Iyanuoluwa007/zetabot/3d Model/1.jpg

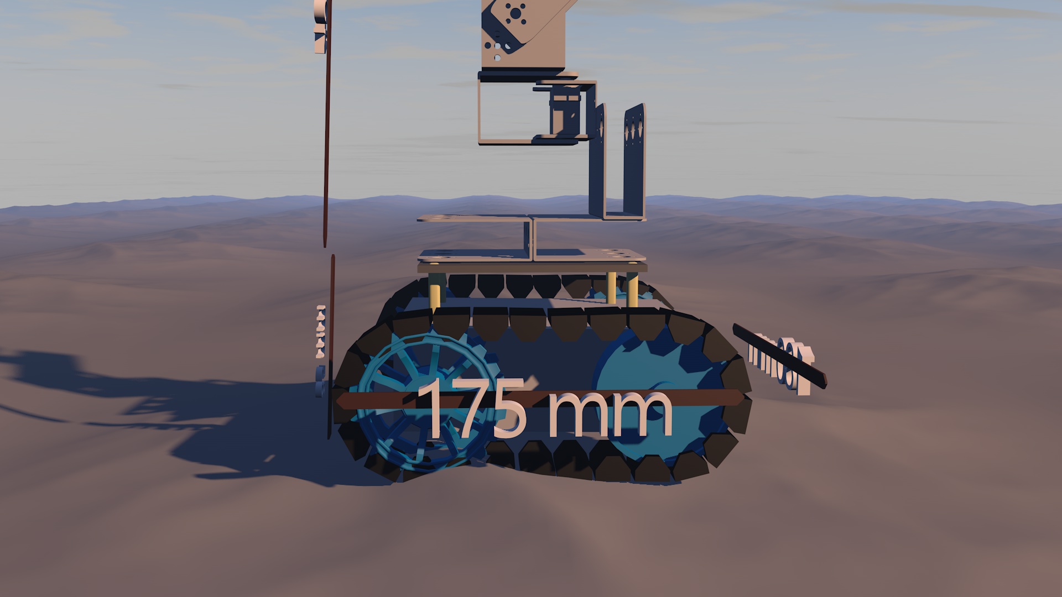
3d Model/1.jpg
