Iyanuoluwa007/zetabot/3d Model/2.jpg

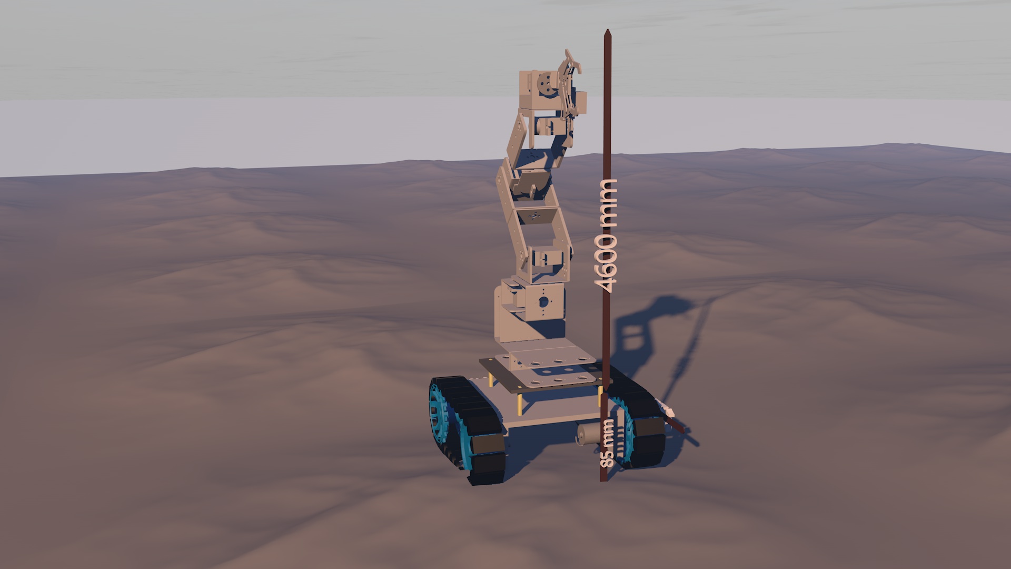
3d Model/2.jpg
