Iyanuoluwa007/zetabot/3d Model/3.jpg

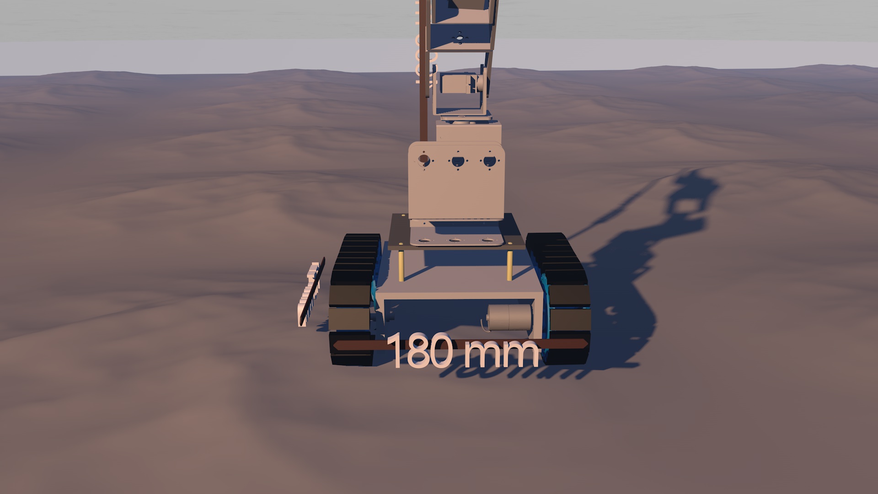
3d Model/3.jpg
