Iyanuoluwa007/zetabot/3d Model/4.jpg

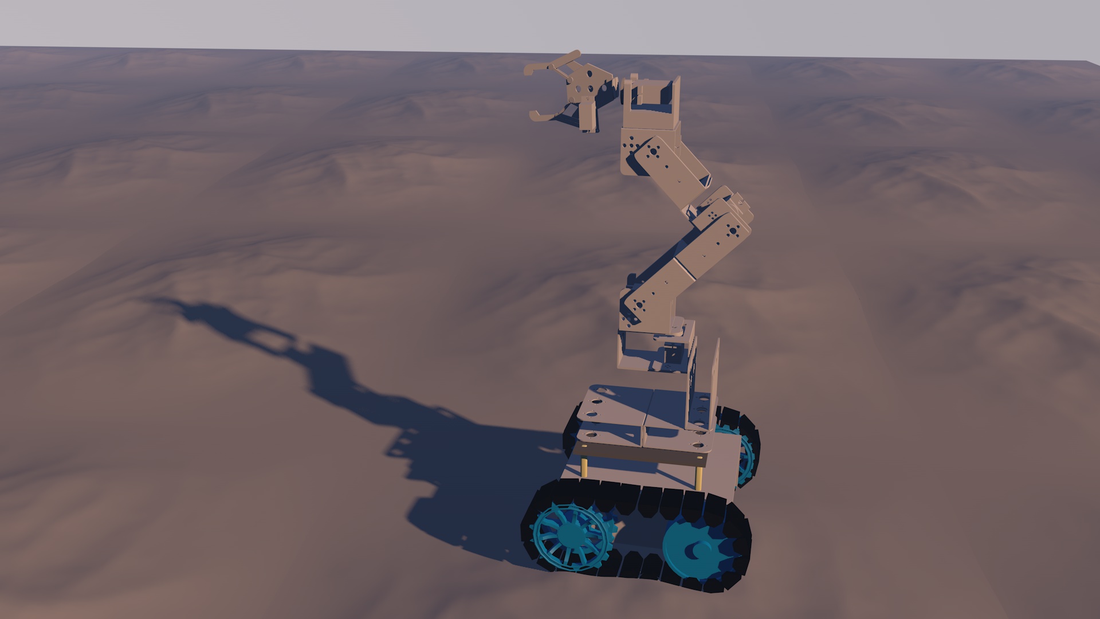
3d Model/4.jpg
