Iyanuoluwa007/zetabot/3d Model/5.jpg

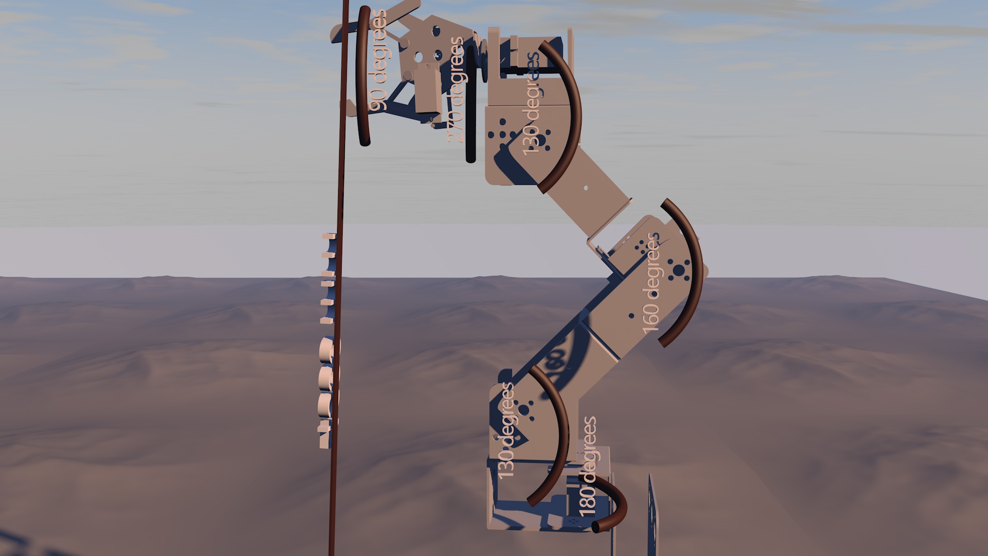
3d Model/5.jpg
