Iyanuoluwa007/zetabot/App/Robotic Arm Controller Code.png

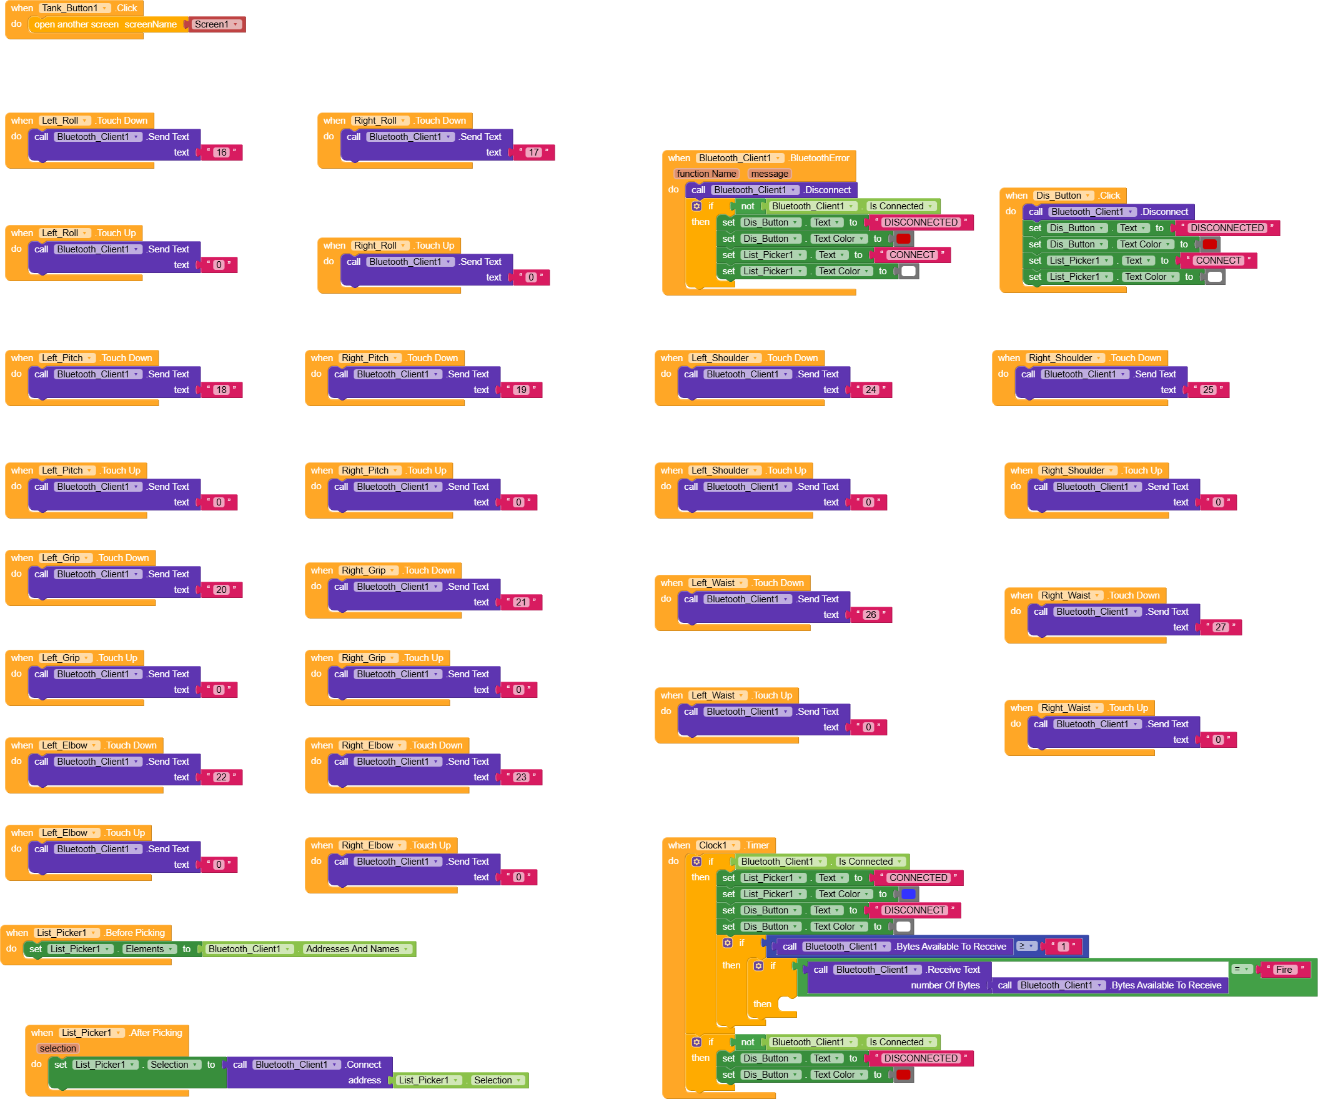
App/Robotic Arm Controller Code.png
