Iyanuoluwa007/zetabot/App/Robotic Tank Controller Code.png

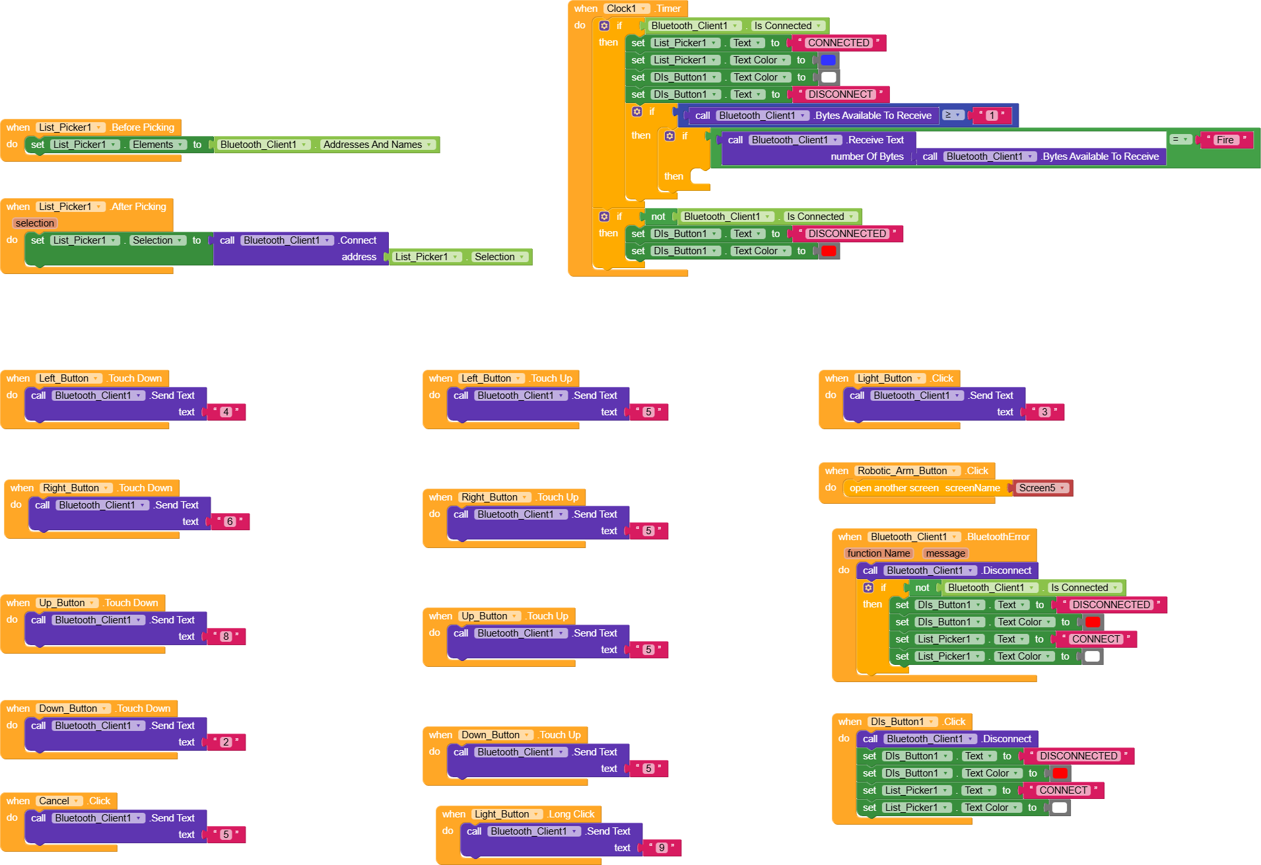
App/Robotic Tank Controller Code.png
