Iyanuoluwa007/zetabot/Documentations/xl6019 module.jpg

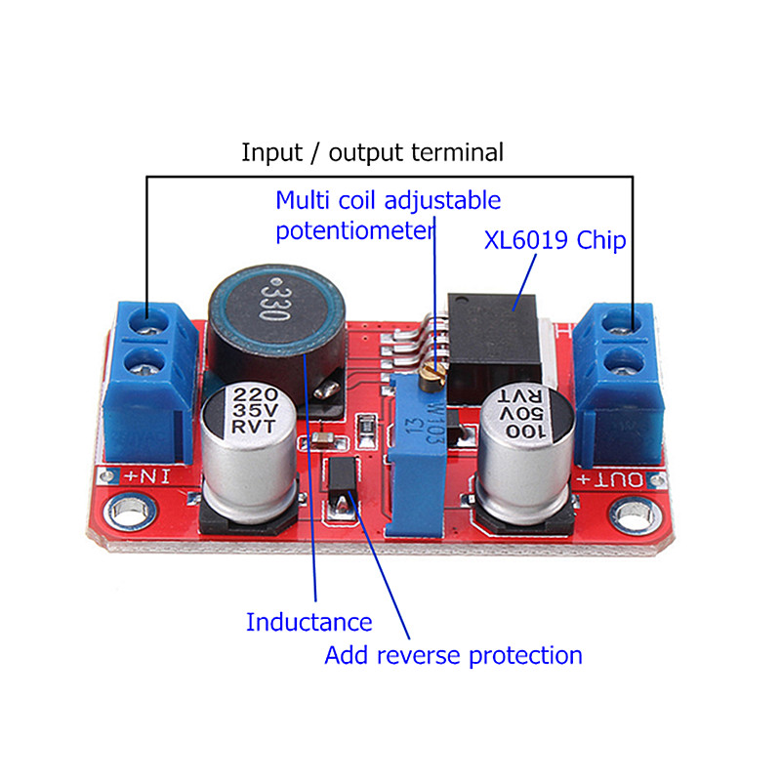
Documentations/xl6019 module.jpg
