Iyanuoluwa007/zetabot/Ideas/iron-ox-farming-robot.jpg

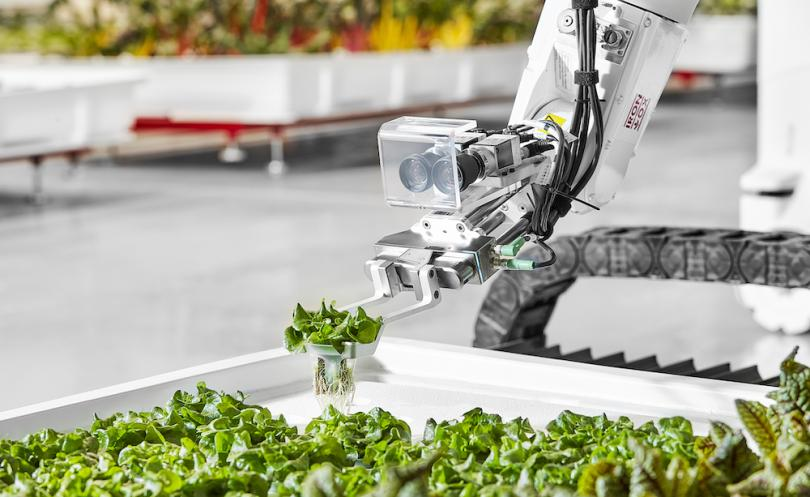
Ideas/iron-ox-farming-robot.jpg
