Iyanuoluwa007/zetabot/Plans/Robot ARM/ARM.jpg

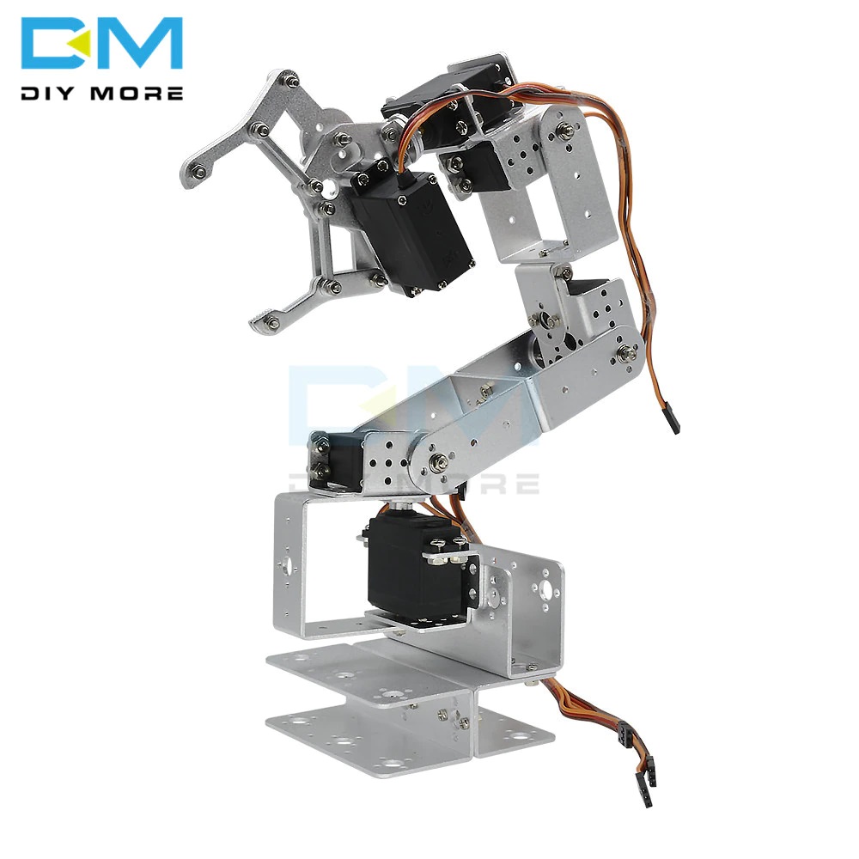
Plans/Robot ARM/ARM.jpg
