Iyanuoluwa007/zetabot/Plans/Robot ARM/H266de6f652d54e7d96e25e7c5b8f142fn.webp

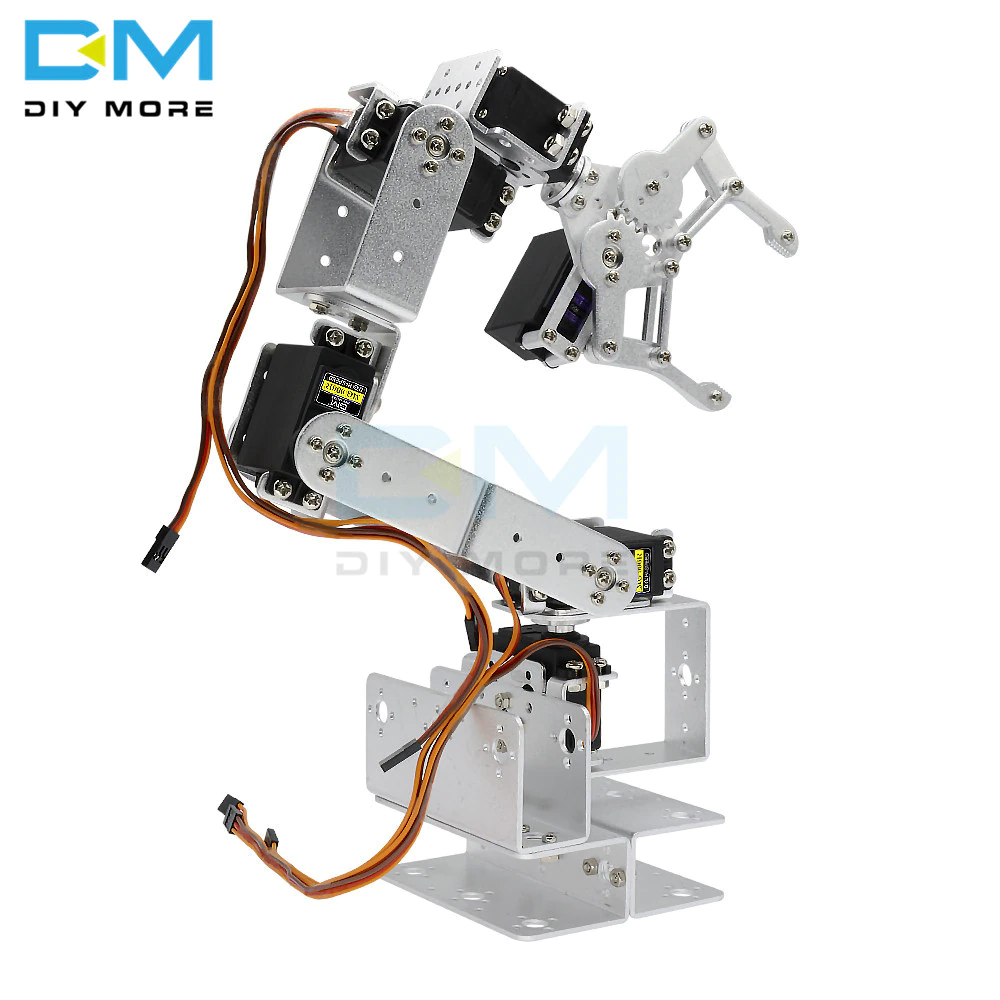
Plans/Robot ARM/H266de6f652d54e7d96e25e7c5b8f142fn.webp
