Iyanuoluwa007/zetabot/Plans/Tank/HTB1DEFNXvvsK1RjSspdq6AZepXag.webp

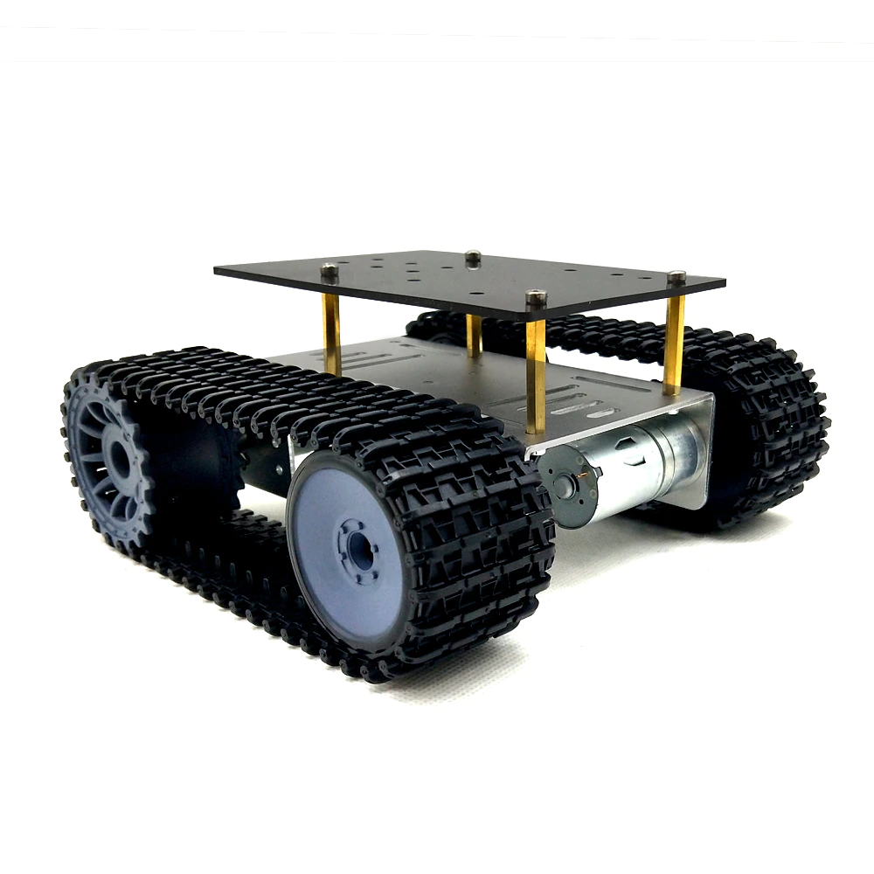
Plans/Tank/HTB1DEFNXvvsK1RjSspdq6AZepXag.webp
