Iyanuoluwa007/zetabot/Plans/Tank/HTB1HbVOXynrK1Rjy1Xcq6yeDVXaf.webp

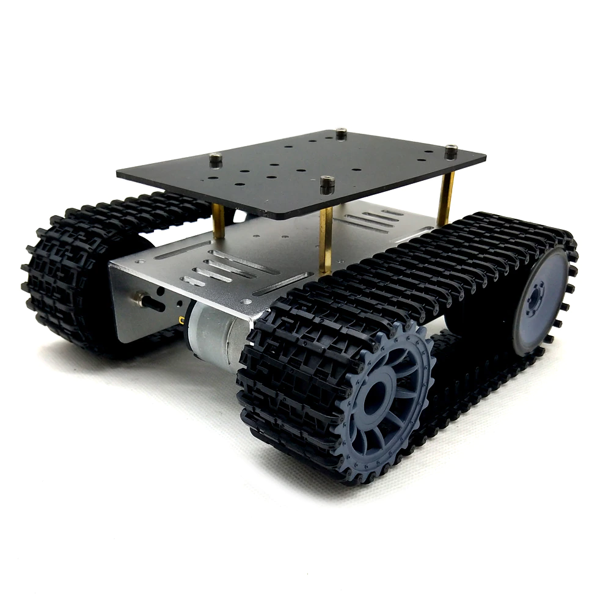
Plans/Tank/HTB1HbVOXynrK1Rjy1Xcq6yeDVXaf.webp
