Iyanuoluwa007/zetabot/Plans/Tank/HTB1tVsih6TpK1RjSZKPq6y3UpXaW.webp

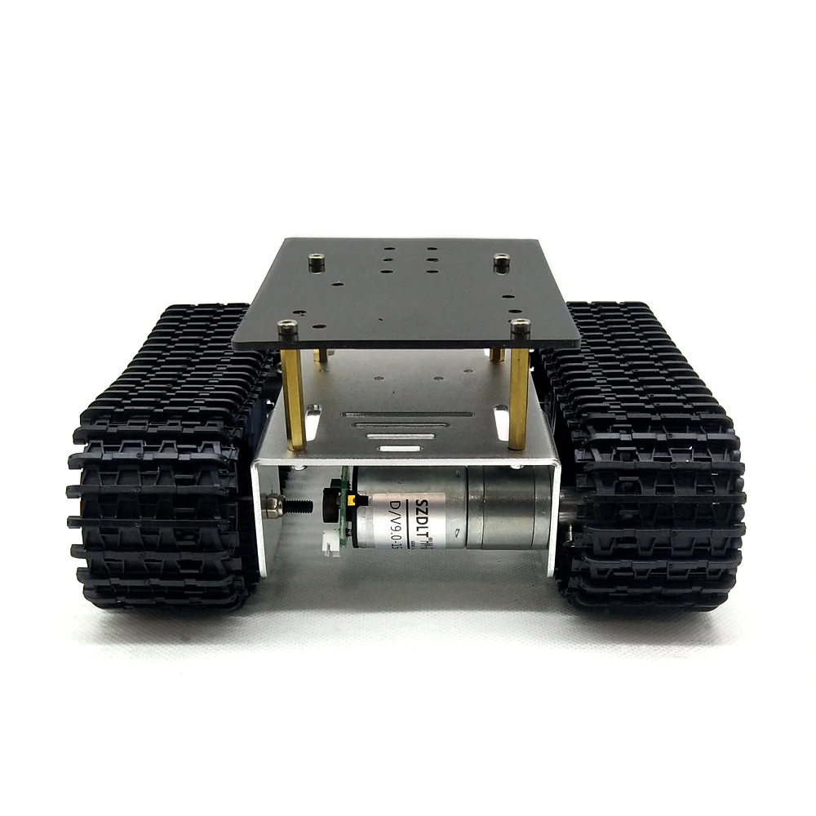
Plans/Tank/HTB1tVsih6TpK1RjSZKPq6y3UpXaW.webp
