Iyanuoluwa007/zetabot/Plans/Tank/Motor Specifications.jpg

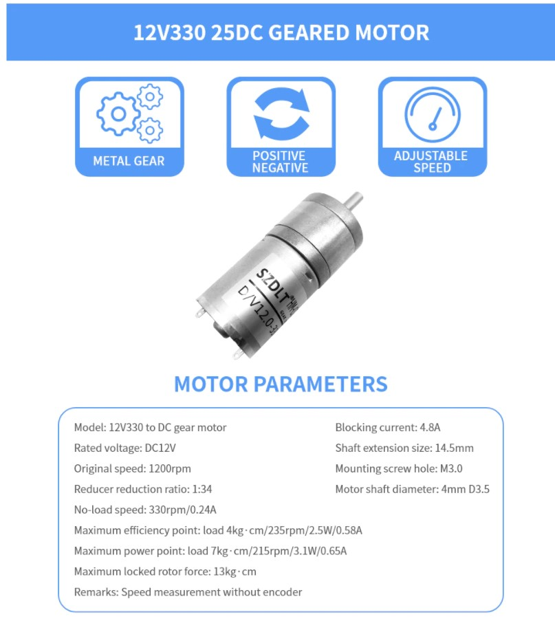
Plans/Tank/Motor Specifications.jpg
