Iyanuoluwa007/zetabot/Building/20210622_141823.jpg

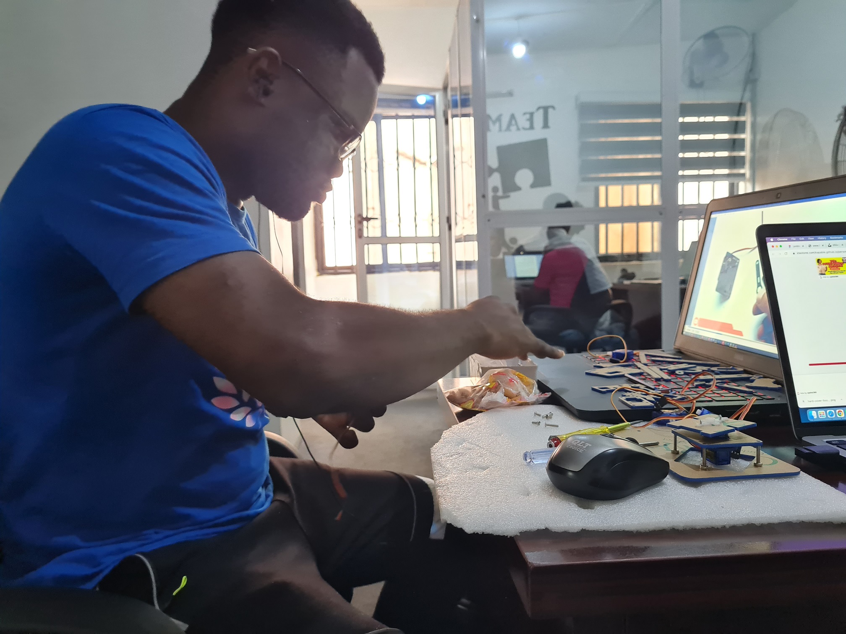
Building/20210622_141823.jpg
