Iyanuoluwa007/zetabot/Building/20210622_141831.jpg

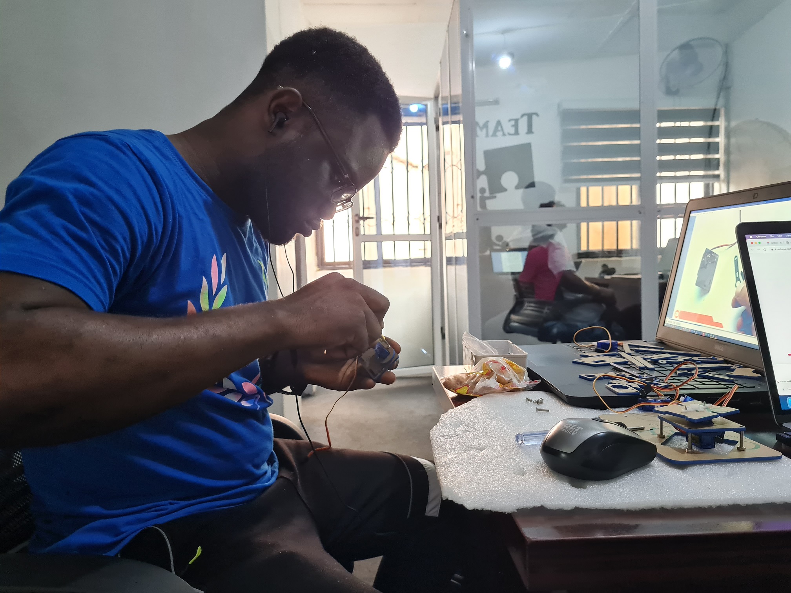
Building/20210622_141831.jpg
