Iyanuoluwa007/zetabot/Building/20210623_141826_01_saved.jpg

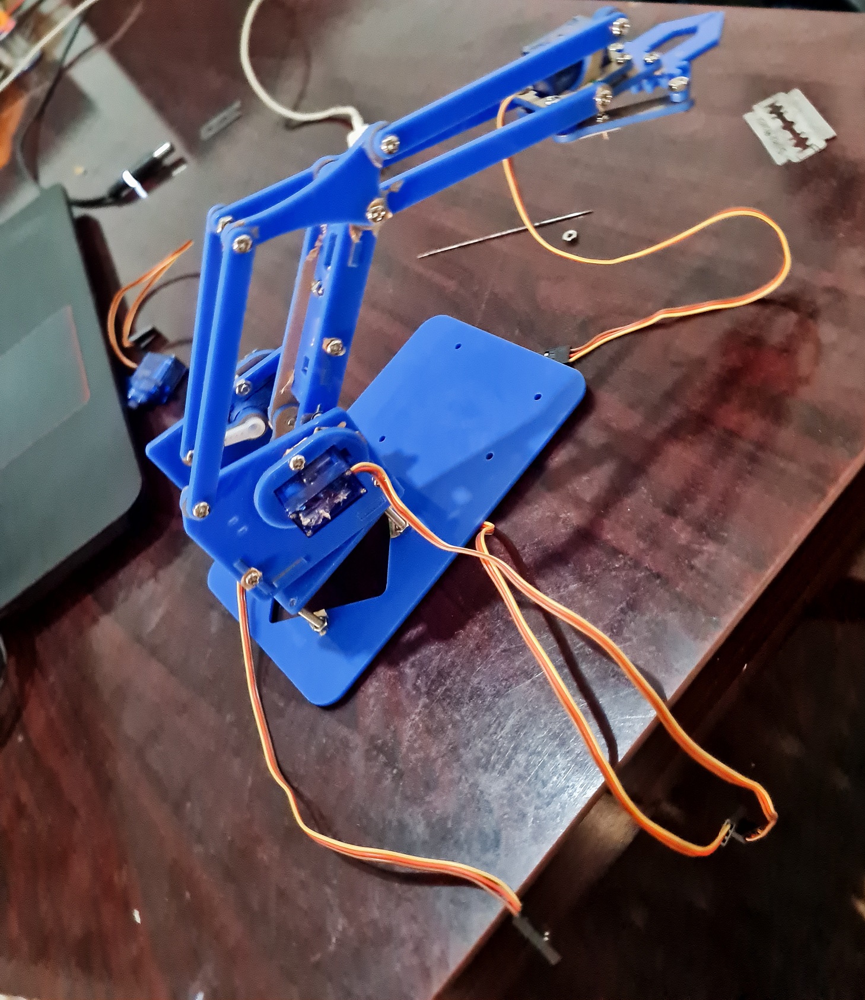
Building/20210623_141826_01_saved.jpg
