Iyanuoluwa007/zetabot/Building/20210712_181845.jpg

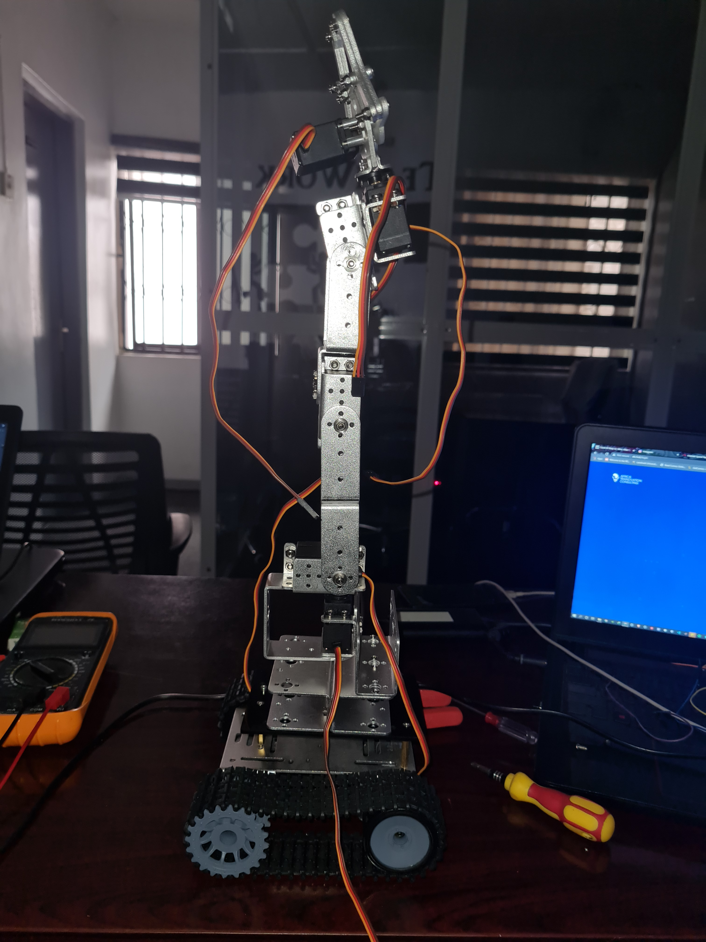
Building/20210712_181845.jpg
