Iyanuoluwa007/zetabot/Building/20210727_150847.jpg

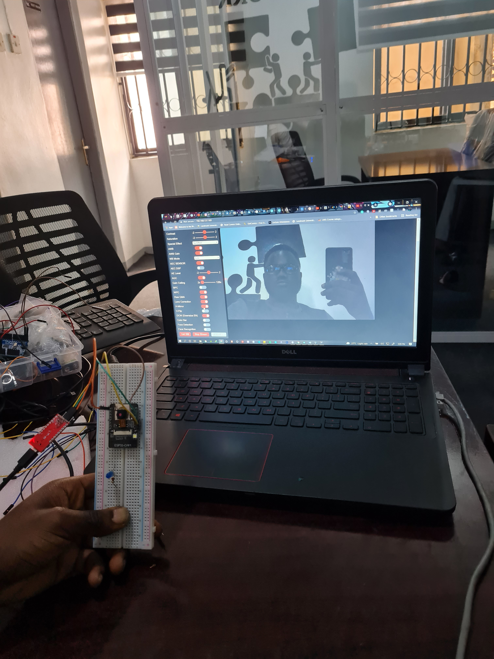
Building/20210727_150847.jpg
