Iyanuoluwa007/zetabot/Building/20210728_153554.jpg

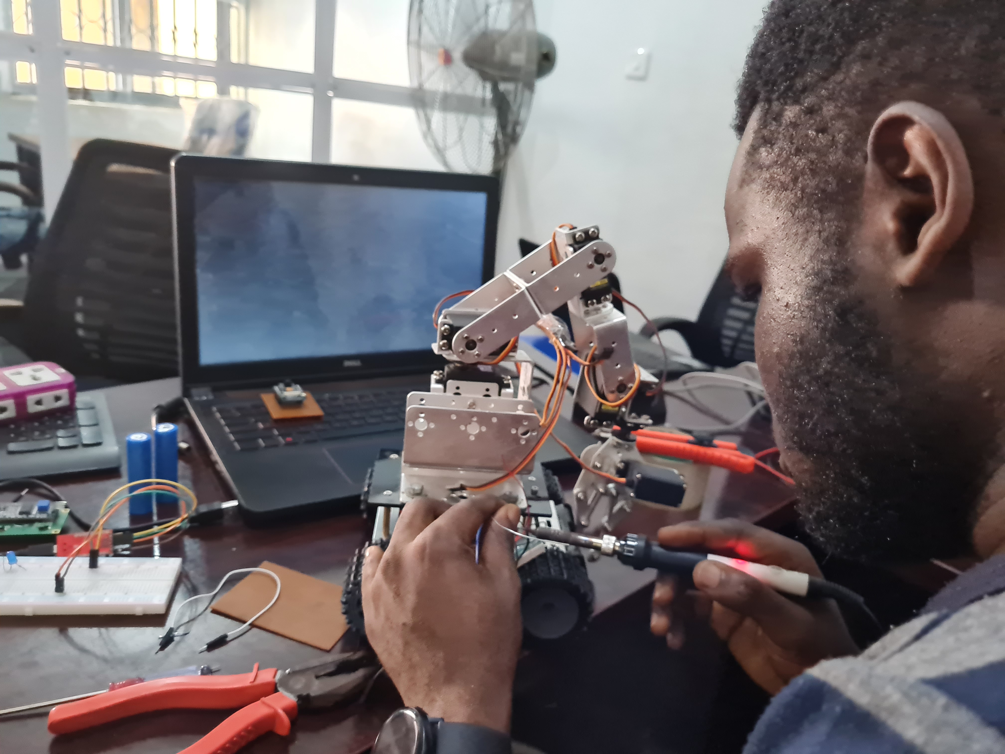
Building/20210728_153554.jpg
