Iyanuoluwa007/zetabot/Building/20210729_151537.jpg

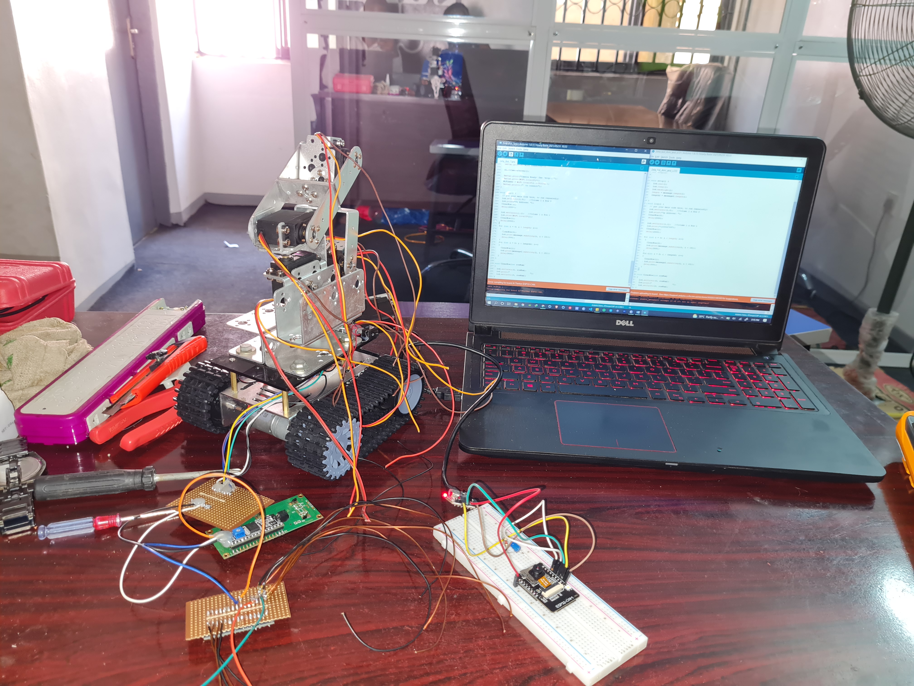
Building/20210729_151537.jpg
