Iyanuoluwa007/zetabot/Building/20210729_151607_01_saved.jpg

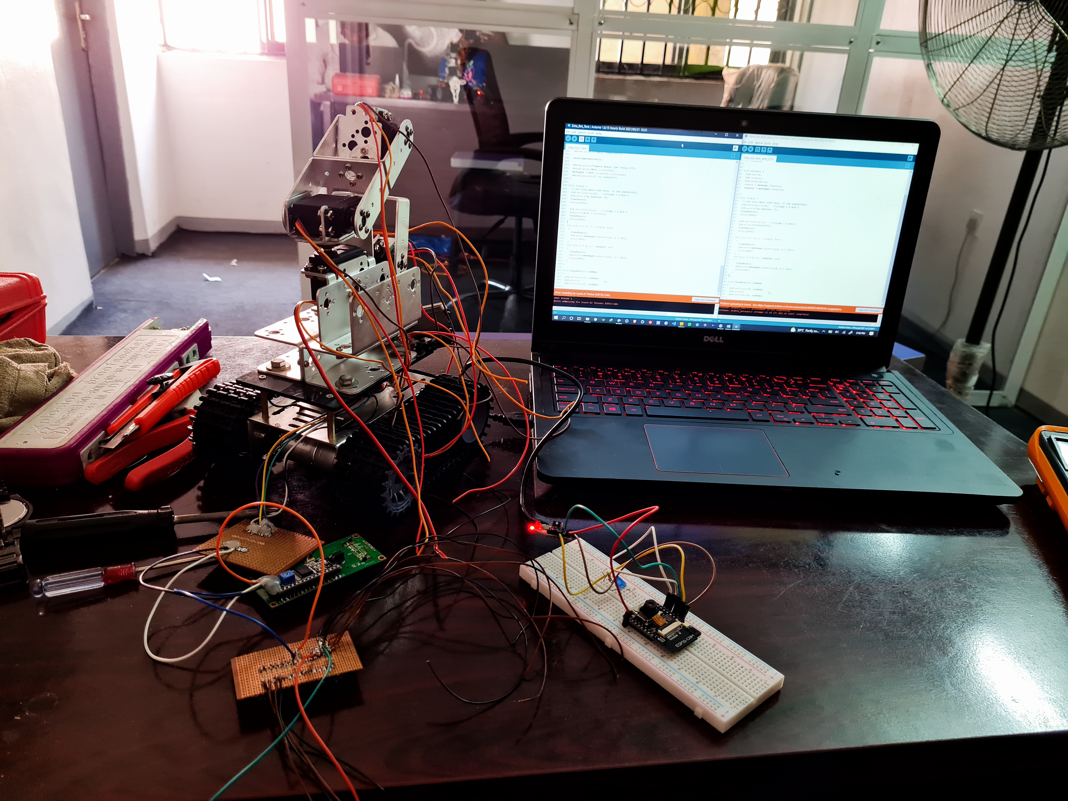
Building/20210729_151607_01_saved.jpg
