Iyanuoluwa007/zetabot/Building/20210729_181653.jpg

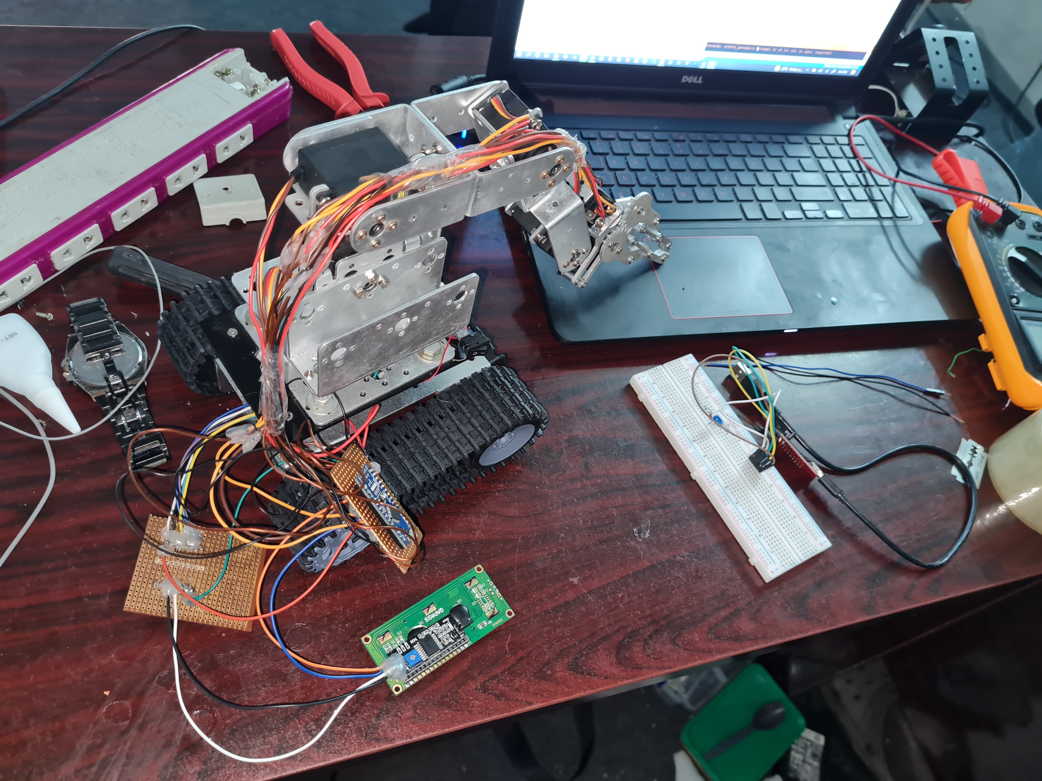
Building/20210729_181653.jpg
