Iyanuoluwa007/zetabot/Building/20210729_181700.jpg

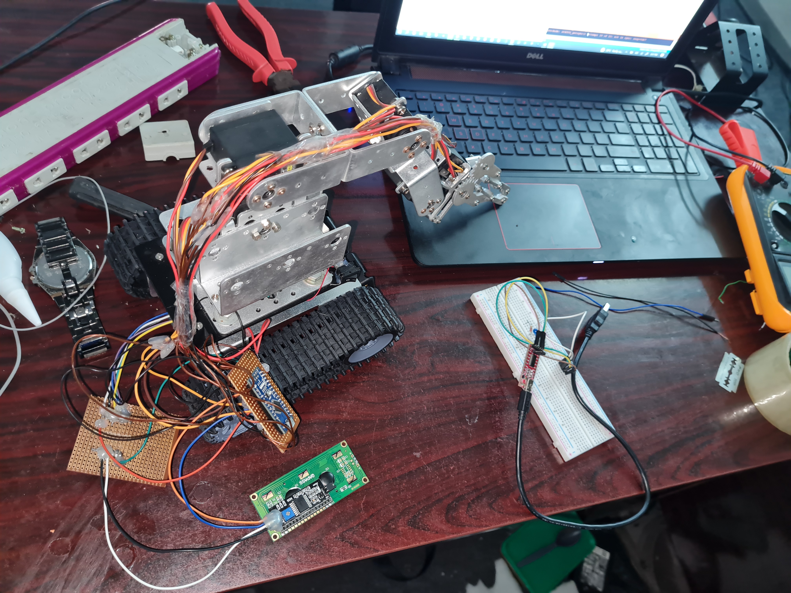
Building/20210729_181700.jpg
