Iyanuoluwa007/zetabot/Building/20210807_152206.jpg

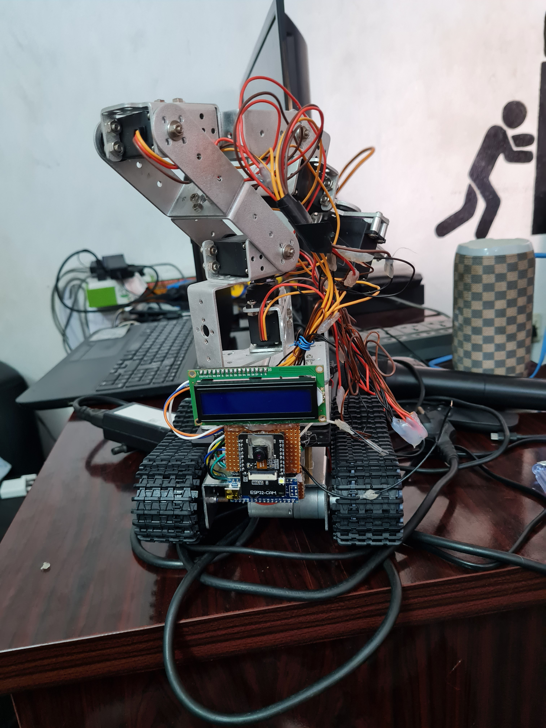
Building/20210807_152206.jpg
