Iyanuoluwa007/zetabot/Failures/20210814_111013.jpg

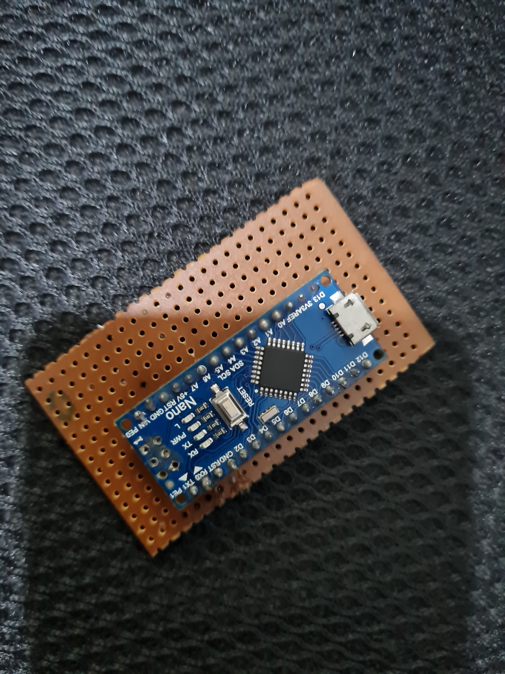
Failures/20210814_111013.jpg
