Iyanuoluwa007/zetabot/Failures/20210814_111018.jpg

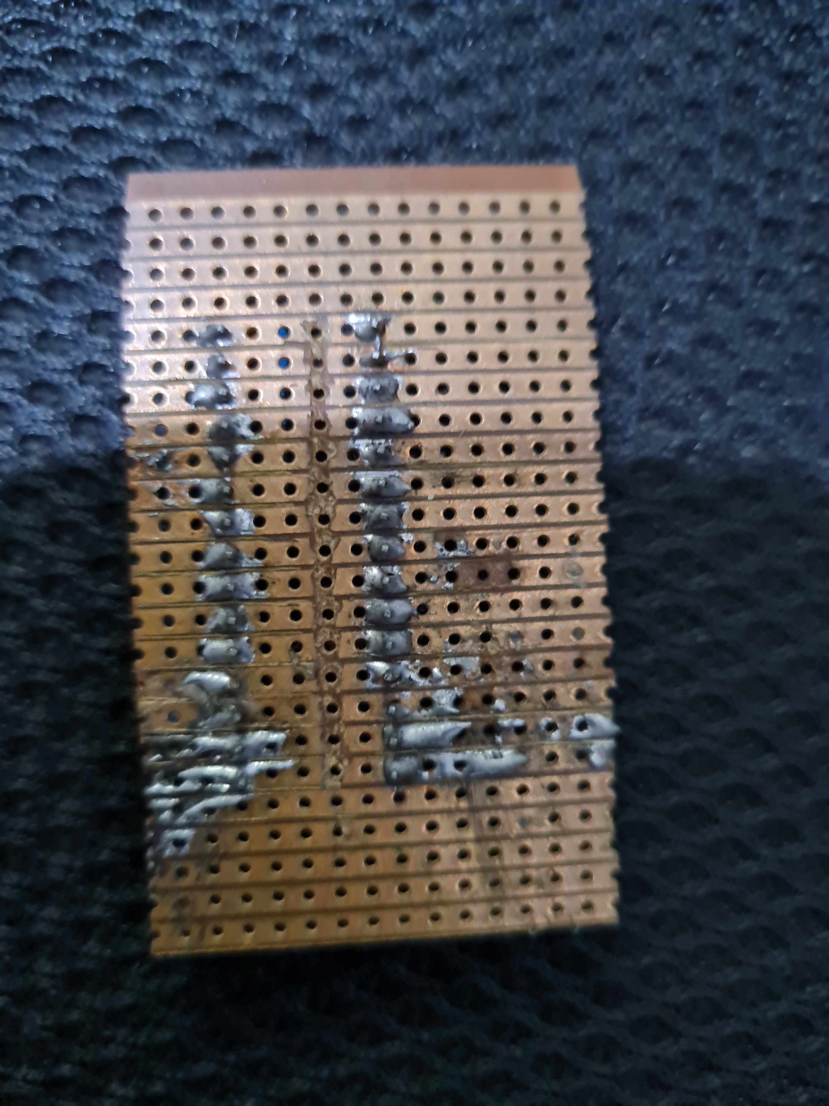
Failures/20210814_111018.jpg
