Iyanuoluwa007/zetabot/Failures/20210814_111028.jpg

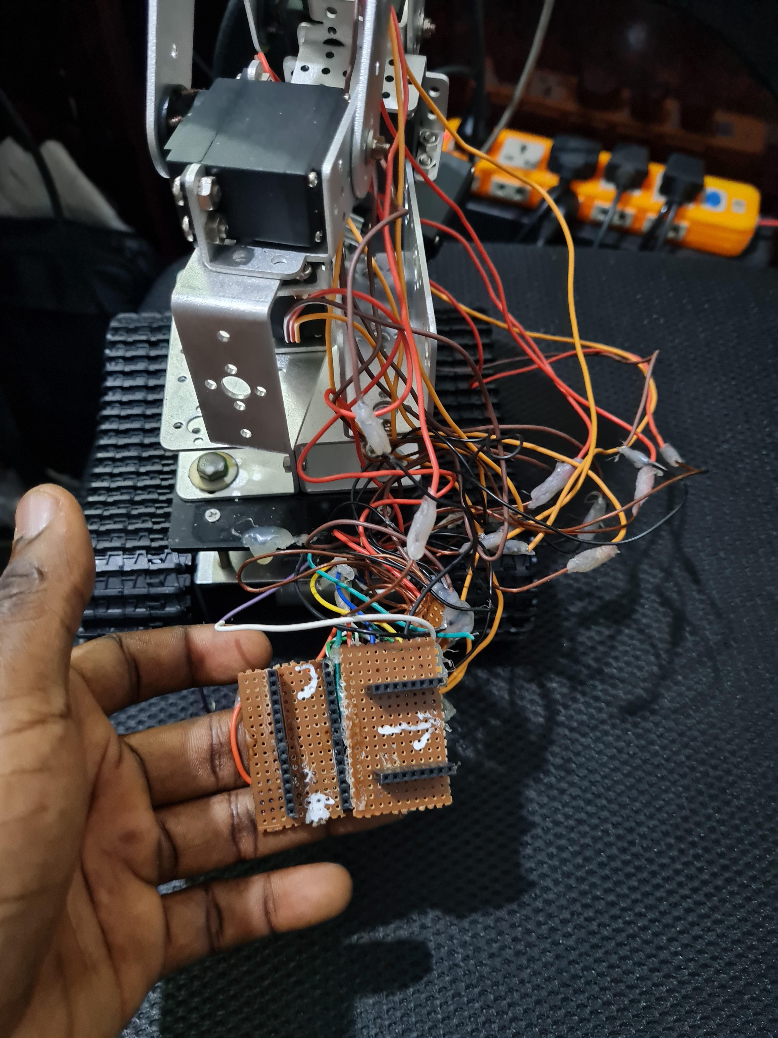
Failures/20210814_111028.jpg
