Iyanuoluwa007/zetabot/Failures/20210814_111034.jpg

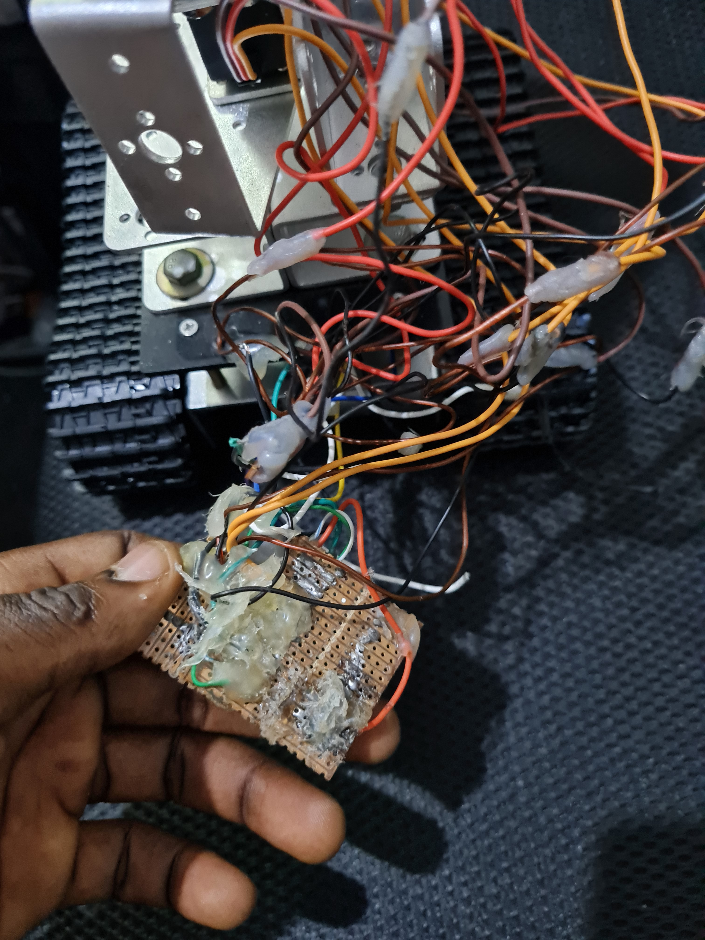
Failures/20210814_111034.jpg
