Iyanuoluwa007/zetabot/Failures/20210815_182547_01_saved.jpg

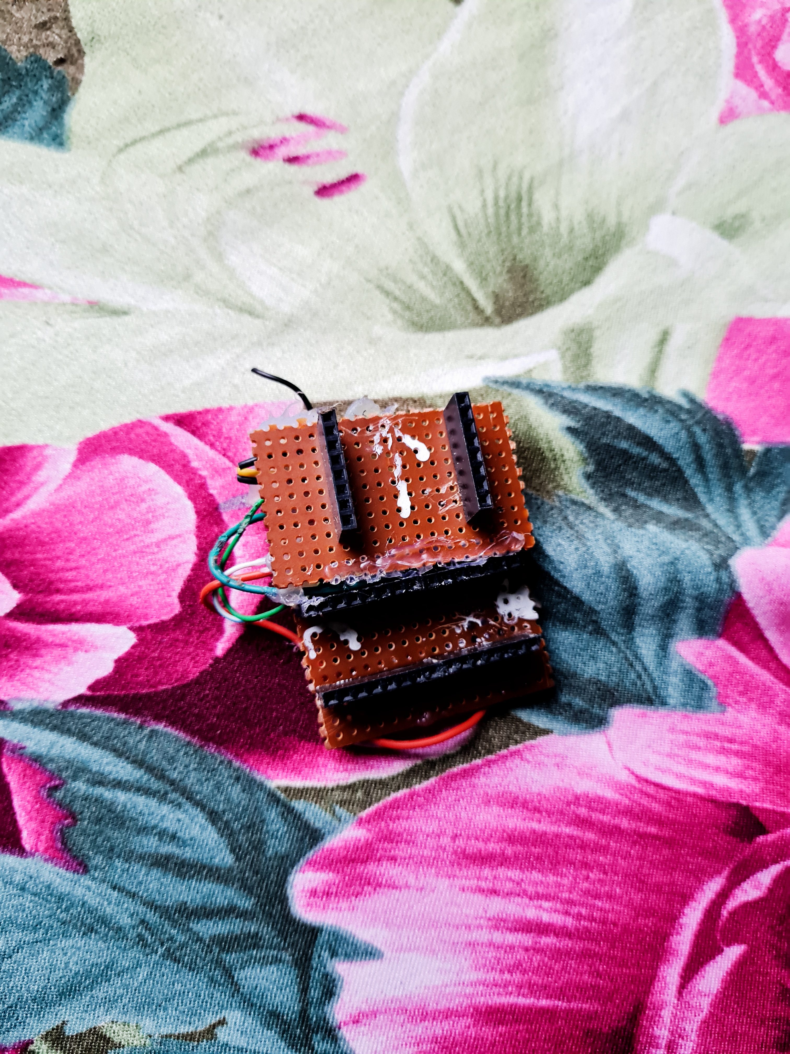
Failures/20210815_182547_01_saved.jpg
