Iyanuoluwa007/zetabot/Failures/20210815_182602_01_saved.jpg

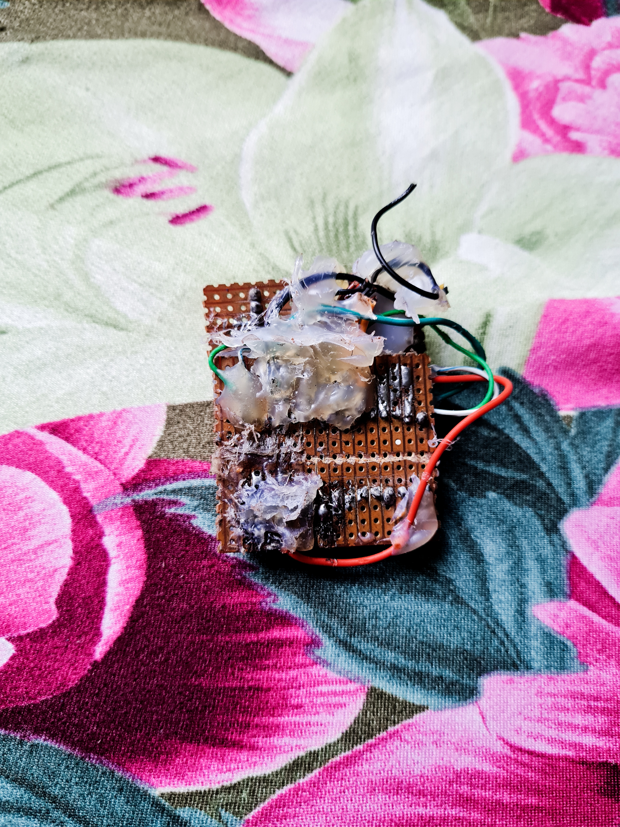
Failures/20210815_182602_01_saved.jpg
